AidanHockey5/MegaBlaster2/src/logo.h

//Want to make a custom logo?
//Create a 128x64, monochome 1-bit (Only black and white, no greyscale or color) BMP image
//Use a service like this to convert it to XBM https://convertio.co/bmp-xbm/
//Open the XBM file in a text editor and paste-in the data portion (ignore the hight, width, and variable name. Just replace the data)
#ifndef __LOGO_H__
#define __LOGO_H__


#define logo_width 128
#define logo_height 64
#include <Arduino.h>

static uint8_t logo[] = {
  0x00, 0x80, 0xFF, 0xFF, 0x01, 0xC0, 0xFF, 0xFF, 0x00, 0xFE, 0xFF, 0xFF, 
  0x7F, 0x00, 0x00, 0x00, 0x00, 0x80, 0xFF, 0xFF, 0x03, 0xE0, 0xFF, 0xFF, 
  0x00, 0xFE, 0xFF, 0xFF, 0xFF, 0x07, 0x00, 0x00, 0x00, 0x80, 0xFF, 0xFF, 
  0x07, 0xF0, 0xFF, 0xFF, 0x00, 0xFE, 0xFF, 0xFF, 0xFF, 0x1F, 0x00, 0x00, 
  0x00, 0x80, 0xFF, 0xFF, 0x07, 0xF0, 0xFF, 0xFF, 0x00, 0xFE, 0xFF, 0xFF, 
  0xFF, 0x3F, 0x00, 0x00, 0x00, 0x80, 0xFF, 0xFF, 0x0F, 0xF8, 0xFF, 0xFF, 
  0x00, 0xFE, 0xFF, 0xFF, 0xFF, 0x7F, 0x00, 0x00, 0x00, 0x80, 0xFF, 0xFF, 
  0x1F, 0xFC, 0xFF, 0xFF, 0x00, 0xFE, 0xFF, 0xFF, 0xFF, 0xFF, 0x00, 0x00, 
  0x00, 0x80, 0xFF, 0xFF, 0x3F, 0xFE, 0xFF, 0xFF, 0x00, 0xFE, 0xFF, 0xFF, 
  0xFF, 0xFF, 0x00, 0x00, 0x00, 0x80, 0xFF, 0xFF, 0x7F, 0xFF, 0xFF, 0xFF, 
  0x00, 0xFE, 0xFF, 0xFF, 0xFF, 0xFF, 0x01, 0x00, 0x00, 0x80, 0xFF, 0xFF, 
  0xFF, 0xFF, 0xFF, 0xFF, 0x00, 0xFE, 0xFF, 0xFF, 0xFF, 0xFF, 0x01, 0x00, 
  0x00, 0x80, 0xFF, 0xFF, 0xFF, 0xFF, 0xFF, 0xFF, 0x00, 0xFE, 0xFF, 0xC7, 
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
//   0xFF, 0xFF, 0xFD, 0xFF, 0xFF, 0xF7, 0xFF, 0x03, 0xC0, 0x07, 0x00, 0x00, 
//   0x00, 0xE0, 0x0F, 0xE0, 0xFF, 0xFF, 0xFD, 0xFF, 0xFF, 0xF7, 0xFF, 0x07, 
//   0xC0, 0x0F, 0x00, 0x00, 0x80, 0xC0, 0x0F, 0xF0, 0xFF, 0xFF, 0xFD, 0xFF, 
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

  #endif
